AndreiBertescu/Sensor_Hut/SensorHut_V2/3D models/Used parts/OKY3501-5 Voltage Regulator.step

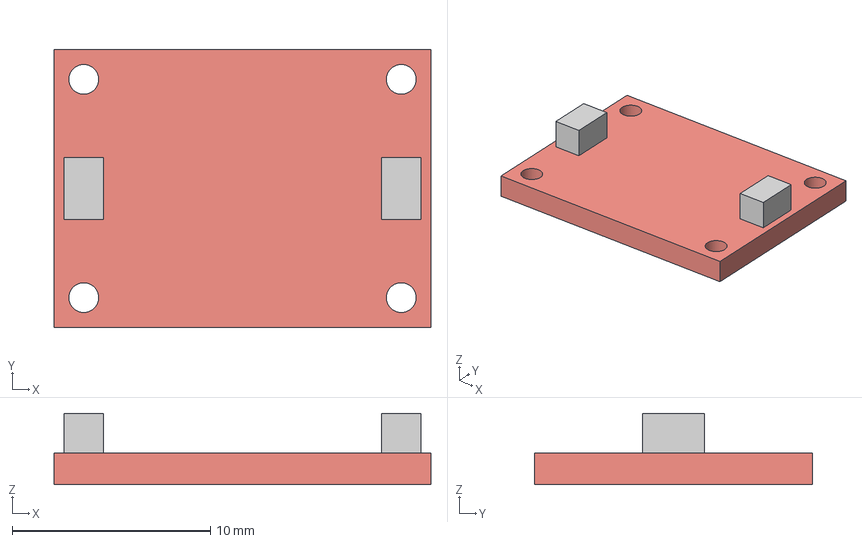
[picture p24: CAD file, 2025-04-27]
SensorHut_V2/3D models/Used parts/OKY3501-5 Voltage Regulator.step
19.0 x 14.0 x 3.60 mm
