AndreiBertescu/Sensor_Hut/SensorHut_V2/3D models/Used parts/DHT11.step

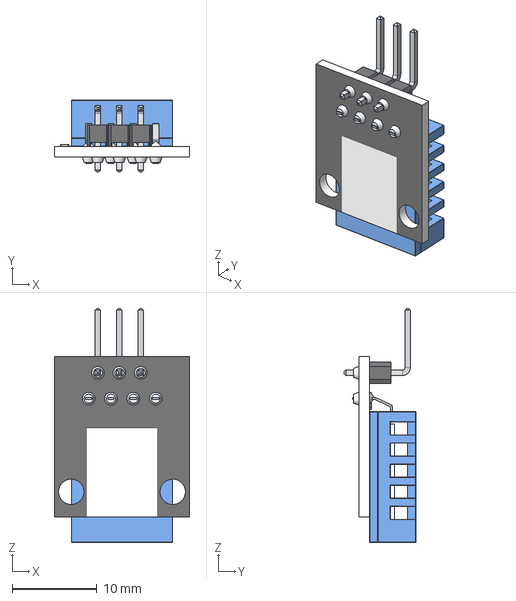
[picture p25: CAD file, 2025-04-27]
SensorHut_V2/3D models/Used parts/DHT11.step
16.0 x 8.50 x 27.7 mm
