AndreiBertescu/Sensor_Hut/SensorHut_V2/3D models/Used parts/Buzzer.stp

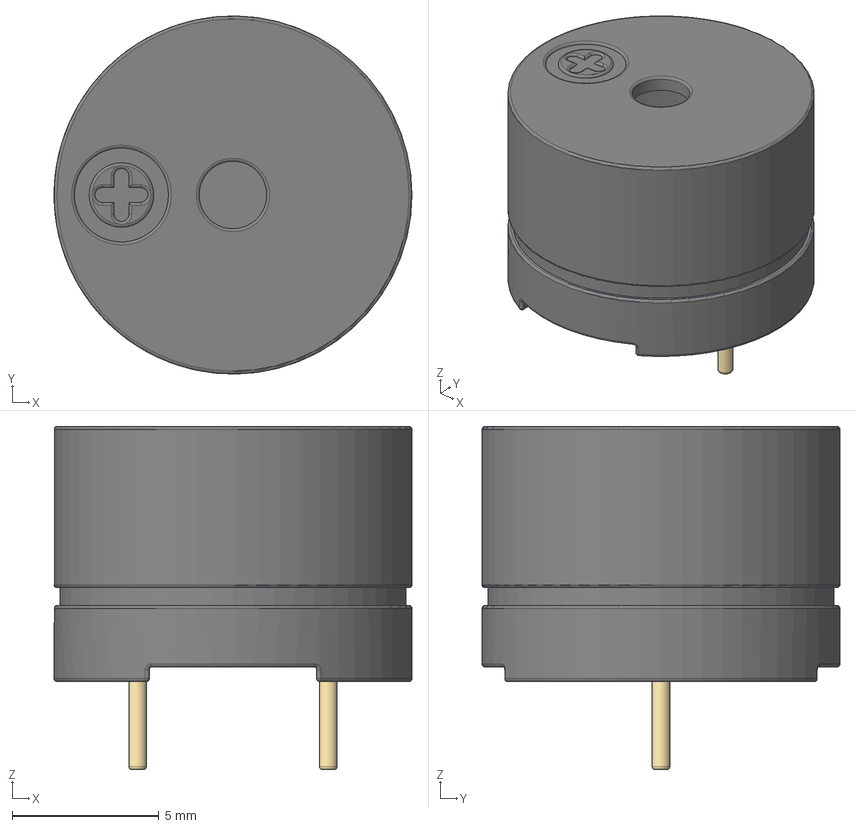
[picture p28: CAD file, 2025-04-27]
SensorHut_V2/3D models/Used parts/Buzzer.stp
12.2 x 12.2 x 11.7 mm
