AndreiBertescu/Sensor_Hut/SensorHut_V2/3D models/Used parts/Header connectors/female/DS1023-1x6SF11.stp

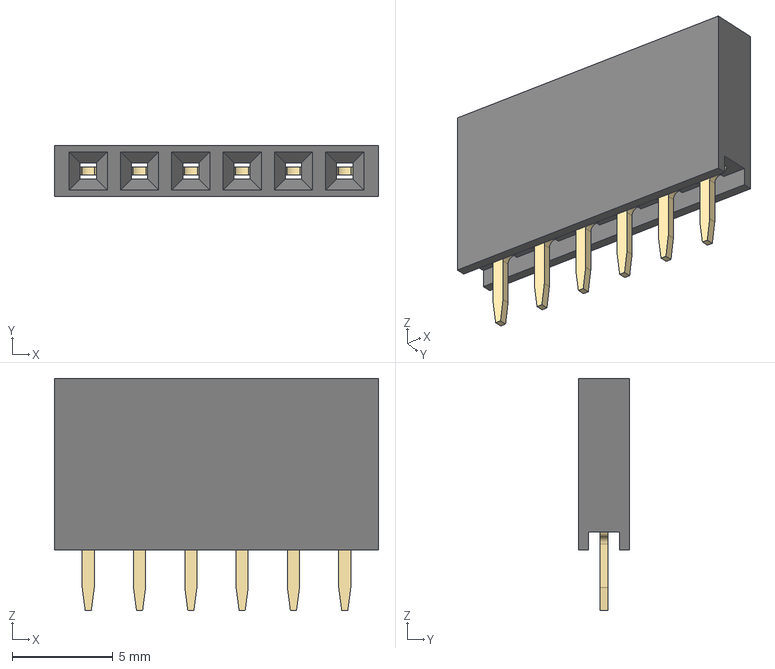
[picture p29: CAD file, 2025-04-27]
SensorHut_V2/3D models/Used parts/Header connectors/female/DS1023-1x6SF11.stp
16.0 x 2.54 x 11.5 mm
