AndreiBertescu/Sensor_Hut/SensorHut_V2/3D models/Used parts/Header connectors/vertical/2.54mm/DS1021-1x6SF11.stp

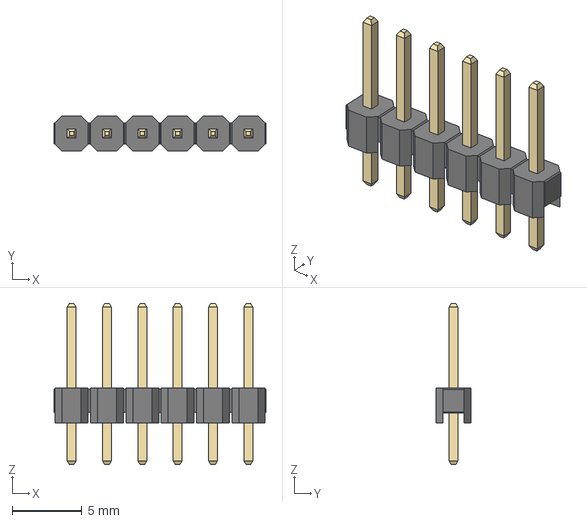
[picture p31: CAD file, 2025-04-27]
SensorHut_V2/3D models/Used parts/Header connectors/vertical/2.54mm/DS1021-1x6SF11.stp
15.2 x 2.54 x 11.6 mm
