AndreiBertescu/Sensor_Hut/SensorHut_V2/3D models/Used parts/Header connectors/female/DS1023-2x8SF11.stp

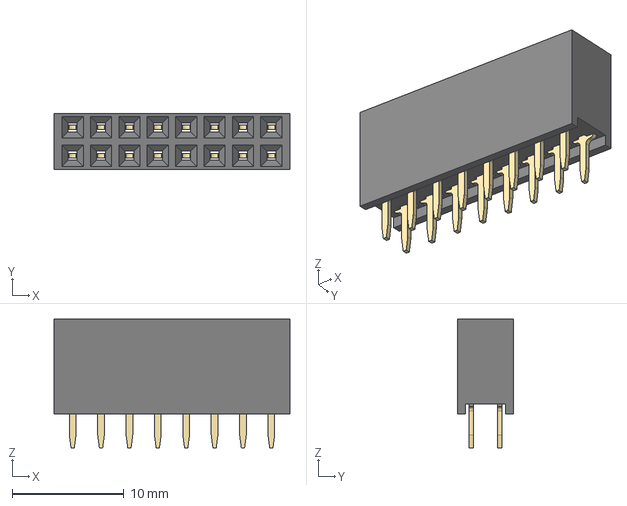
[picture p32: CAD file, 2025-04-27]
SensorHut_V2/3D models/Used parts/Header connectors/female/DS1023-2x8SF11.stp
21.1 x 5.00 x 11.5 mm
