AndreiBertescu/Sensor_Hut/SensorHut_V2/3D models/Used parts/MPPT Solar Controller.step

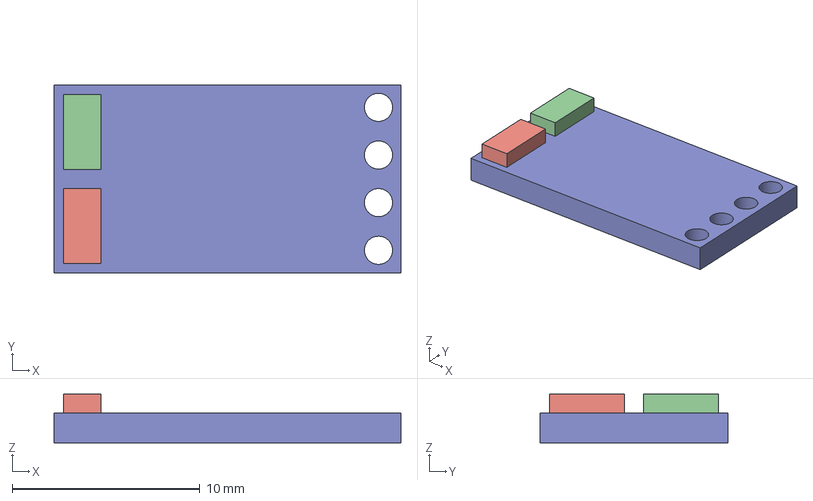
[picture p35: CAD file, 2025-04-27]
SensorHut_V2/3D models/Used parts/MPPT Solar Controller.step
18.5 x 10.0 x 2.60 mm
