AndreiBertescu/Sensor_Hut/SensorHut_V2/3D models/Used parts/Header connectors/vertical/2.54mm/DS1070-6MVV6.stp

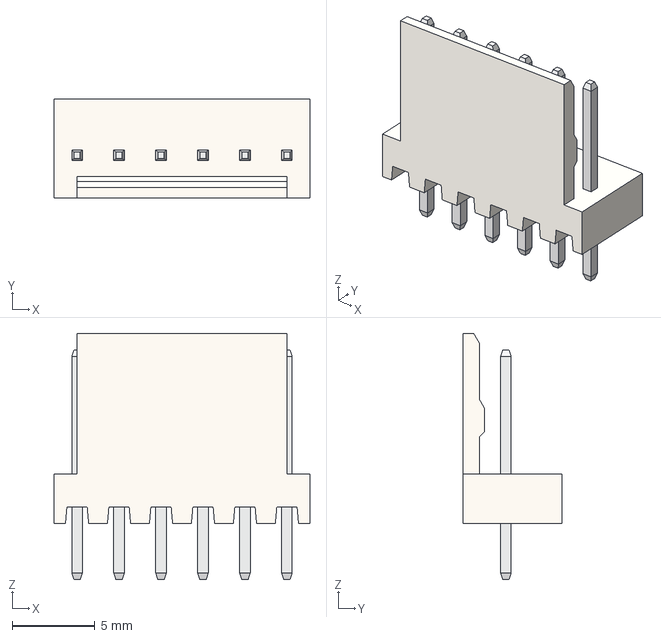
[picture p38: CAD file, 2025-04-27]
SensorHut_V2/3D models/Used parts/Header connectors/vertical/2.54mm/DS1070-6MVV6.stp
15.5 x 6.00 x 14.9 mm
