AndreiBertescu/Sensor_Hut/SensorHut_V2/3D models/Used parts/ST7789.stp

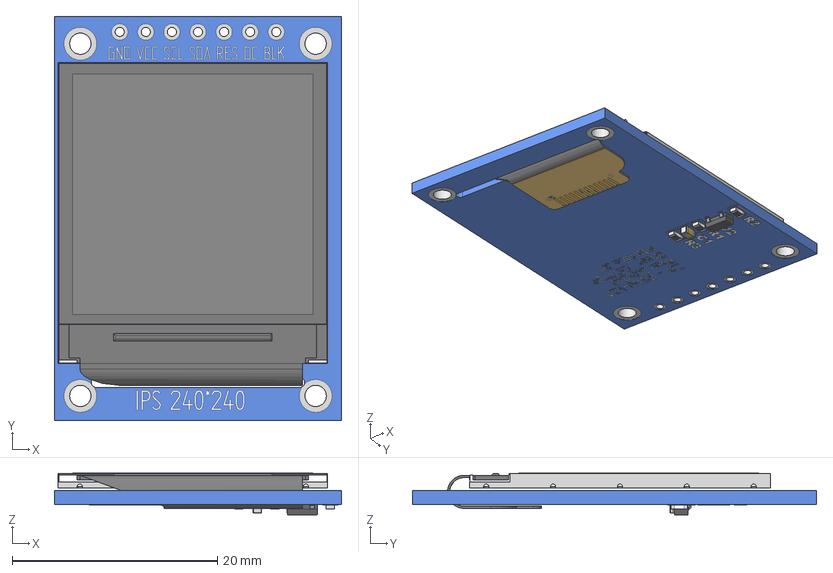
[picture p39: CAD file, 2025-04-27]
SensorHut_V2/3D models/Used parts/ST7789.stp
27.9 x 39.4 x 4.06 mm
1.3 TFT IPS - Board
1.3 TFT IPS - Flush Reverse Mount
0603 Resistor x 3
0603 Capacitor
SOT-23
