AndreiBertescu/Sensor_Hut/SensorHut_V2/3D models/Used parts/Header connectors/right_angle/2.54mm/DS1022-1x9RD61.stp

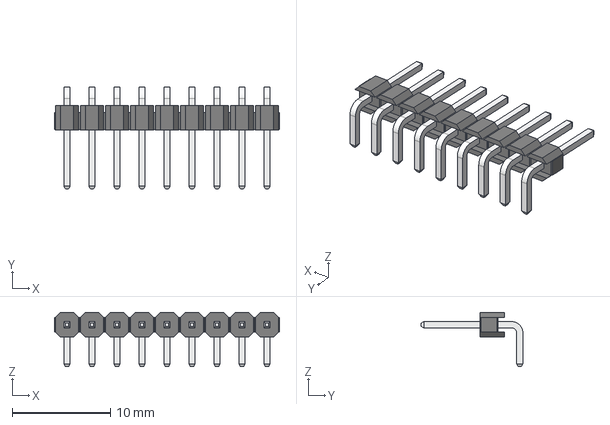
[picture p41: CAD file, 2025-04-27]
SensorHut_V2/3D models/Used parts/Header connectors/right_angle/2.54mm/DS1022-1x9RD61.stp
22.9 x 10.4 x 5.50 mm
