AndreiBertescu/Sensor_Hut/SensorHut_V2/3D models/Used parts/RES-0.125W-H-CF.stp

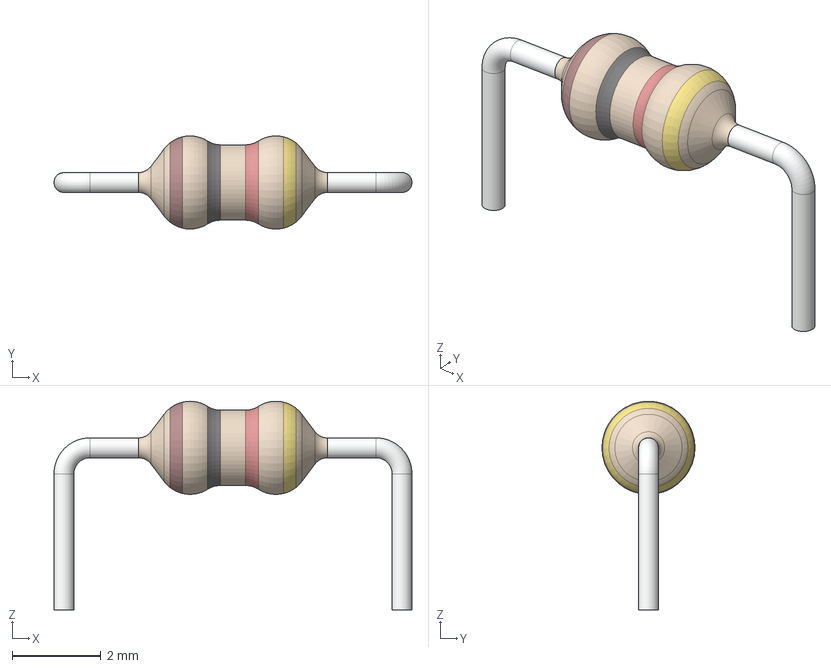
[picture p43: CAD file, 2025-04-27]
SensorHut_V2/3D models/Used parts/RES-0.125W-H-CF.stp
8.07 x 2.10 x 4.70 mm
