AndreiBertescu/Sensor_Hut/SensorHut_V2/3D models/Used parts/Header connectors/vertical/2.54mm/4_PIN_PWM.stp

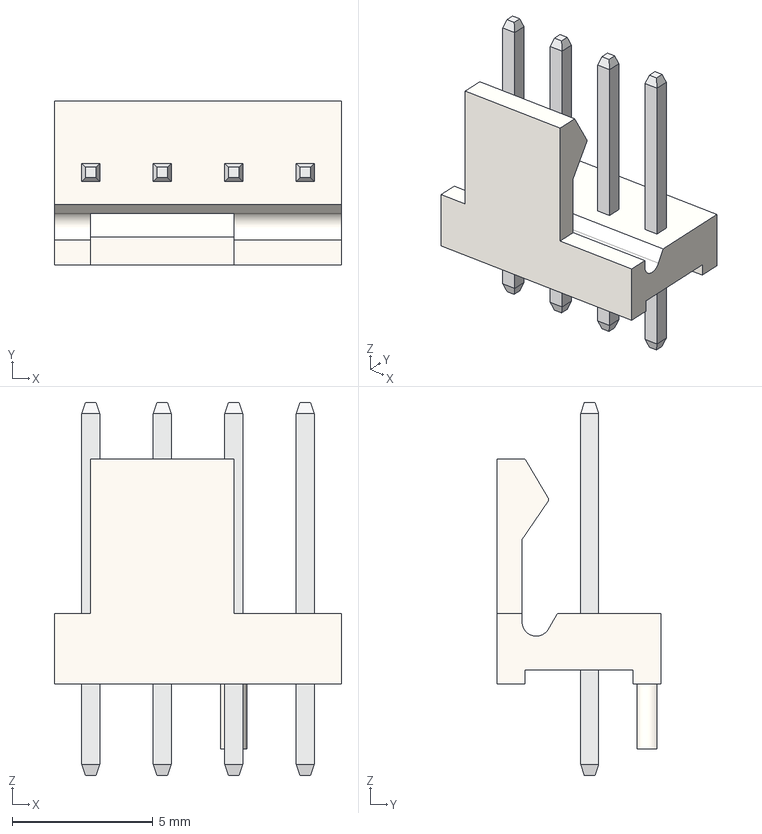
[picture p46: CAD file, 2025-04-27]
SensorHut_V2/3D models/Used parts/Header connectors/vertical/2.54mm/4_PIN_PWM.stp
10.2 x 5.84 x 13.2 mm
