AndreiBertescu/Sensor_Hut/SensorHut_V2/3D models/Used parts/Header connectors/female/DS1023-2x5SF11.stp

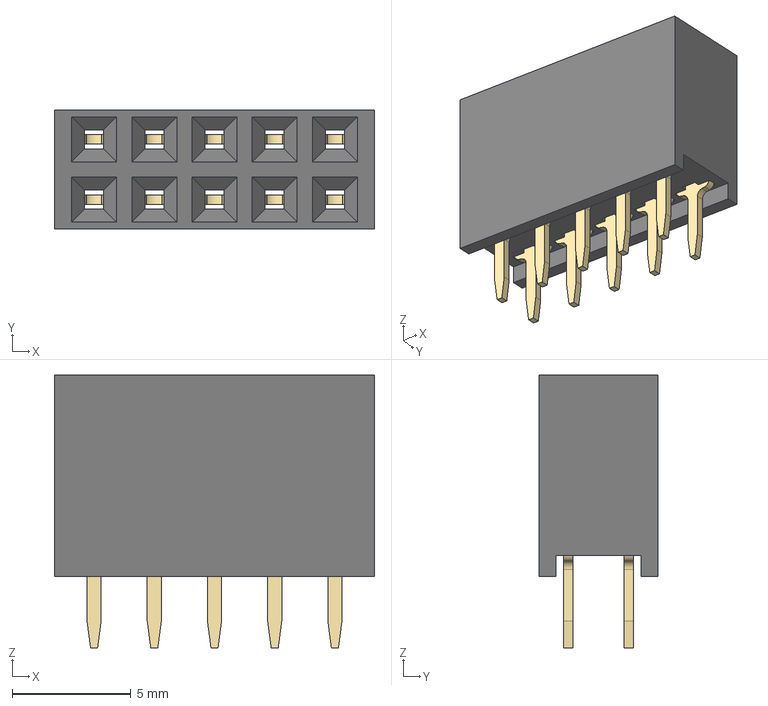
[picture p47: CAD file, 2025-04-27]
SensorHut_V2/3D models/Used parts/Header connectors/female/DS1023-2x5SF11.stp
13.5 x 5.00 x 11.5 mm
