AndreiBertescu/Sensor_Hut/SensorHut_V2/3D models/Used parts/Header connectors/right_angle/2.54mm/DS1070-2MRV6B.stp

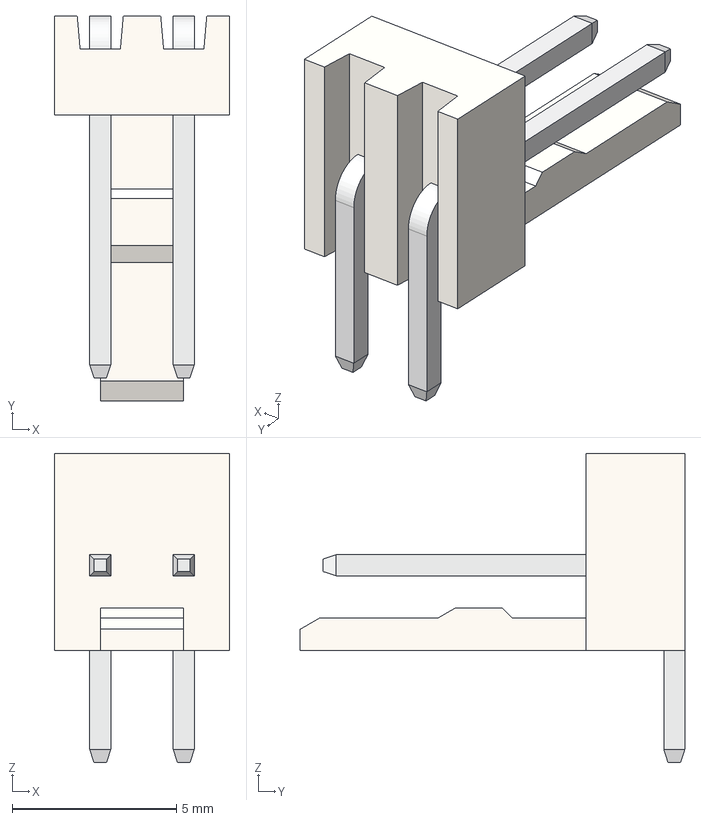
[picture p48: CAD file, 2025-04-27]
SensorHut_V2/3D models/Used parts/Header connectors/right_angle/2.54mm/DS1070-2MRV6B.stp
5.33 x 11.7 x 9.40 mm
