AndreiBertescu/Sensor_Hut/SensorHut_V2/3D models/Used parts/SPDT Slide Switch.step

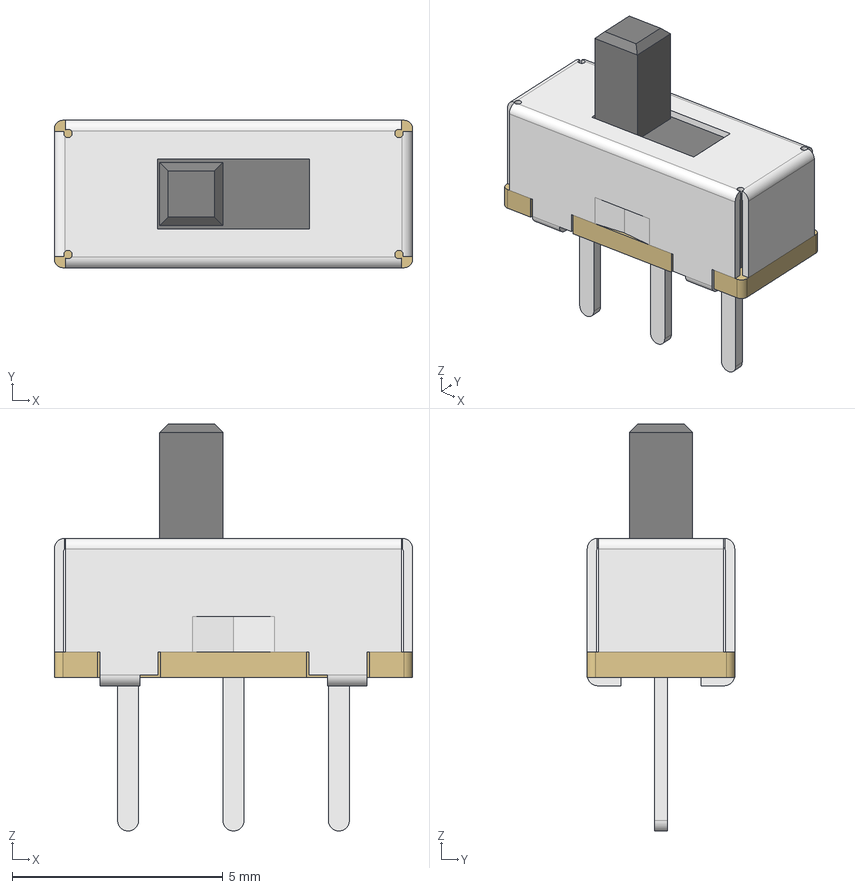
[picture p50: CAD file, 2025-04-27]
SensorHut_V2/3D models/Used parts/SPDT Slide Switch.step
8.50 x 3.50 x 9.66 mm
