AndreiBertescu/Sensor_Hut/SensorHut_V2/3D models/Used parts/BMP280.stp

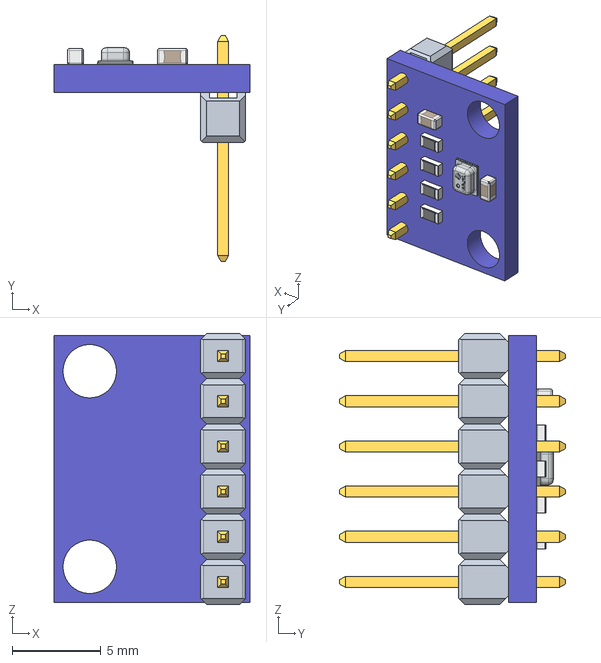
[picture p51: CAD file, 2025-04-27]
SensorHut_V2/3D models/Used parts/BMP280.stp
11.0 x 12.7 x 15.2 mm
