AndreiBertescu/Sensor_Hut/SensorHut_V2/3D models/Used parts/Header connectors/female/DS1023-2x7SF11.stp

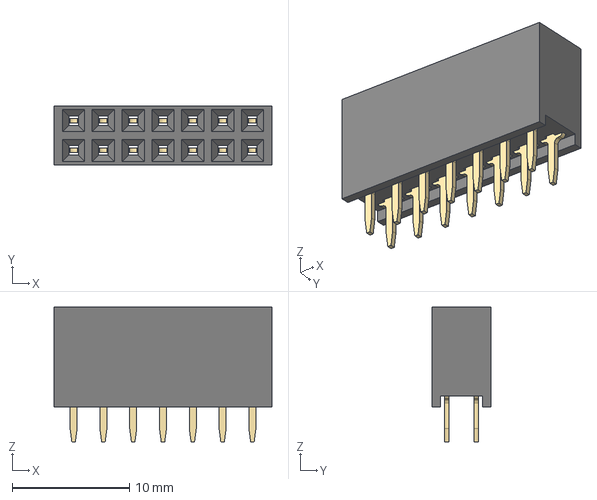
[picture p52: CAD file, 2025-04-27]
SensorHut_V2/3D models/Used parts/Header connectors/female/DS1023-2x7SF11.stp
18.6 x 5.00 x 11.5 mm
