AndreiBertescu/Sensor_Hut/SensorHut_V2/3D models/Used parts/Header connectors/vertical/2.54mm/DS1021-2x1SF11.stp

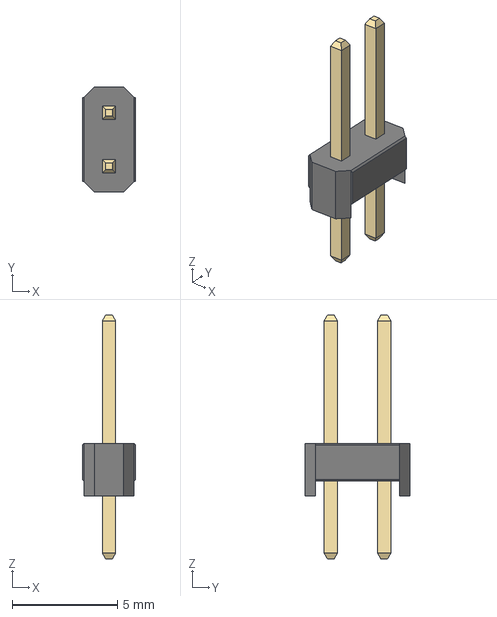
[picture p54: CAD file, 2025-04-27]
SensorHut_V2/3D models/Used parts/Header connectors/vertical/2.54mm/DS1021-2x1SF11.stp
2.54 x 5.00 x 11.6 mm
