AndreiBertescu/Sensor_Hut/SensorHut_V2/3D models/Used parts/Header connectors/vertical/2.54mm/DS1021-1x5S61.stp

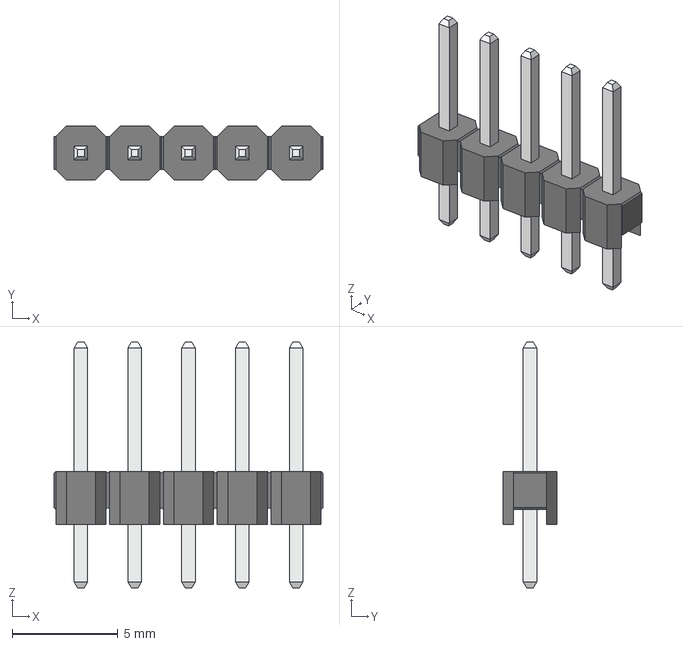
[picture p56: CAD file, 2025-04-27]
SensorHut_V2/3D models/Used parts/Header connectors/vertical/2.54mm/DS1021-1x5S61.stp
12.7 x 2.54 x 11.6 mm
