AndreiBertescu/Sensor_Hut/SensorHut_V2/3D models/Used parts/Tactal Switch 6x6x12mm.stp

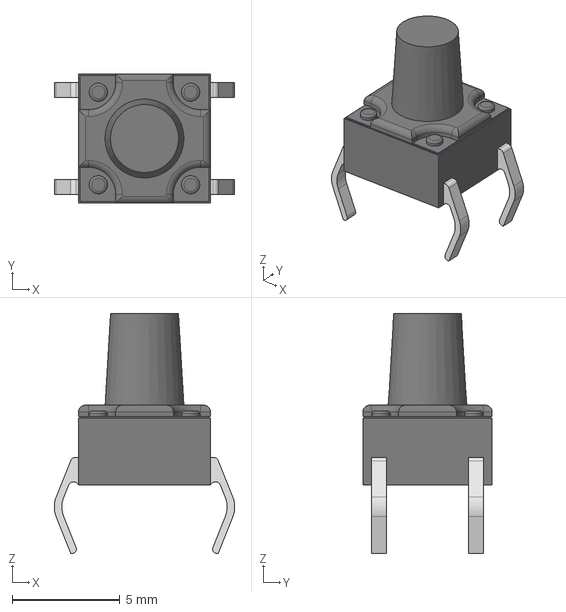
[picture p57: CAD file, 2025-04-27]
SensorHut_V2/3D models/Used parts/Tactal Switch 6x6x12mm.stp
8.37 x 5.99 x 11.1 mm
