AndreiBertescu/Sensor_Hut/SensorHut_V2/3D models/Used parts/Solar Panel 85X65.STEP

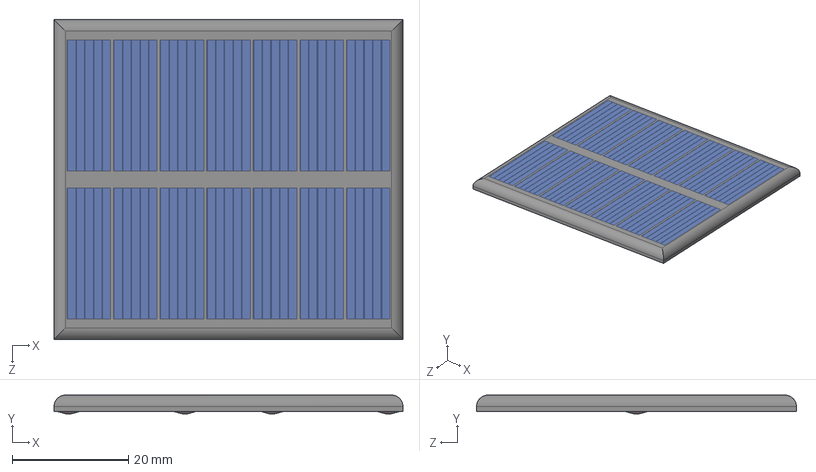
[picture p61: CAD file, 2025-04-27]
SensorHut_V2/3D models/Used parts/Solar Panel 85X65.STEP
60.0 x 3.25 x 55.0 mm
