AndreiBertescu/Sensor_Hut/SensorHut_V2/3D models/Used parts/Header connectors/right_angle/2.54mm/DS1070-6MRV6A.stp

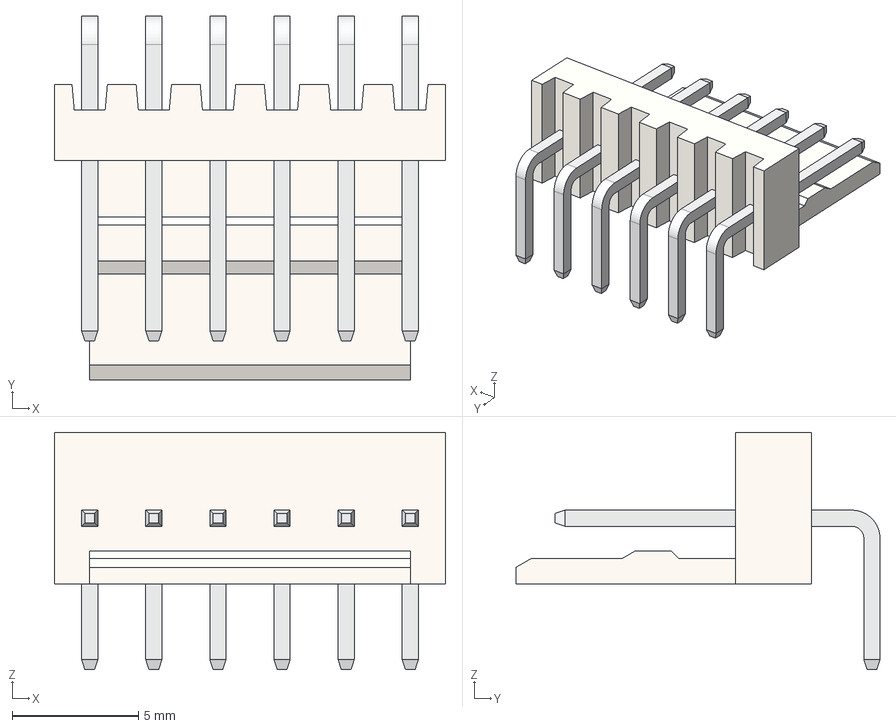
[picture p77: CAD file, 2025-04-27]
SensorHut_V2/3D models/Used parts/Header connectors/right_angle/2.54mm/DS1070-6MRV6A.stp
15.5 x 14.4 x 9.40 mm
