AndreiBertescu/Sensor_Hut/SensorHut_V2/3D models/Used parts/Header connectors/right_angle/2.54mm/DS1070-10MRV6A.stp

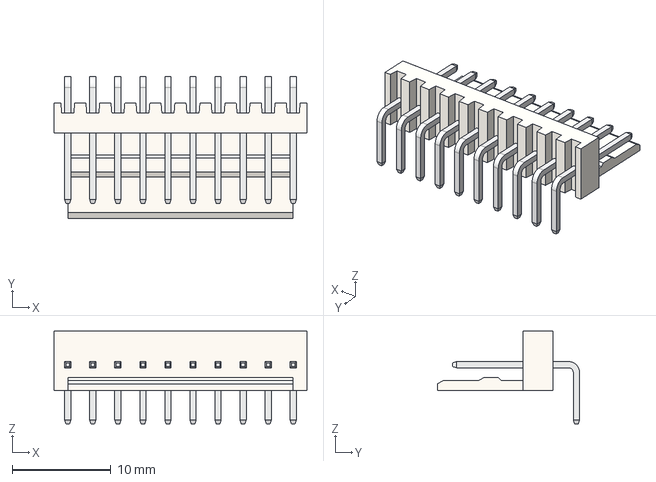
[picture p80: CAD file, 2025-04-27]
SensorHut_V2/3D models/Used parts/Header connectors/right_angle/2.54mm/DS1070-10MRV6A.stp
25.6 x 14.4 x 9.40 mm
