AndreiBertescu/Sensor_Hut/SensorHut_V2/3D models/Used parts/Header connectors/vertical/2.54mm/DS1070-2MVV6.stp

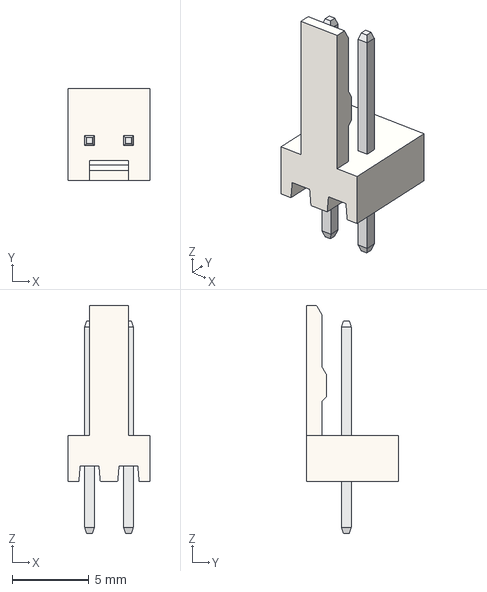
[picture p87: CAD file, 2025-04-27]
SensorHut_V2/3D models/Used parts/Header connectors/vertical/2.54mm/DS1070-2MVV6.stp
5.33 x 6.00 x 14.9 mm
